Edu4Chip/Didactic_PCB/PM_MCU_software/Core/Inc/usefulFunctions.h

/*
 * usefulFunctions.h
 *
 *  Created on: Sep 5, 2024
 *      Author: roope
 */

#ifndef INC_USEFULFUNCTIONS_H_
#define INC_USEFULFUNCTIONS_H_

void USBprintf(const char *fmt, ...);
void smartUSBPrintNext();
void smartUSBPrint(const char *fmt, ...);




#endif /* INC_USEFULFUNCTIONS_H_ */
